hostaboat/alarm_clock/docs/alarm_clock.tex

\documentclass[12pt]{report}

%\usepackage{appendix}

\usepackage[margin=2cm]{geometry}
\geometry{letterpaper}
\setlength{\parindent}{0em}

\usepackage{array,booktabs}

\newcommand{\wood}{Bubinga}
\newcommand{\front}{aluminum}
\newcommand{\project}{Boogie Box}

%%%%%%%%%%%%%%%%%%%%%%%%%%%%%%%%%%%%%%%%%%%%%%%%%%%%%%%%%%%%%%%%%%%%%%%%%%%%%%%%
% Fonts
\usepackage{fontspec}

\newfontfamily\qag{TeX Gyre Adventor}
\newfontfamily\qbk{TeX Gyre Bonum}
\newfontfamily\ssfont[
  Path = fonts/,
  Extension = .ttf,
  UprightFont = *-Italic,
  ItalicFont = *-Italic,
  BoldFont = *-Italic,
  BoldItalicFont = *-Italic,
  Scale = 1.5,
]{DSEG7Classic}
\newfontfamily\ssfontinline[
  Path = fonts/,
  Extension = .ttf,
  UprightFont = *-Italic,
  ItalicFont = *-Italic,
  BoldFont = *-Italic,
  BoldItalicFont = *-Italic,
  Scale = 0.8,
]{DSEG7Classic}
\newfontfamily\ssfontsym[
  Path = fonts/,
  Extension = .ttf,
  UprightFont = *-Italic,
  ItalicFont = *-Italic,
  BoldFont = *-Italic,
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
\begin{tikzpicture}[baseline]
  \node[anchor=base,fill=black!80,draw=black,inner sep=0.7mm,rounded corners=0.5mm]
    {\color{white} \phantom{\ssfontsym #1}};
  \node[anchor=base,inner sep=0.7mm,rounded corners=0.5mm]
    {\color{white} \ssfontsym #2};
\end{tikzpicture}}

% {phantom text}{text}
\newcommand{\sSSDl}[2]{%
\begin{tikzpicture}[baseline]
  \node[anchor=base,fill=black!80,draw=black,inner sep=4pt,rounded corners=0.5mm]
    {\color{white} \phantom{\ssfont #1}};
  \node[anchor=base,inner sep=4pt,rounded corners=0.5mm]
    {\color{white} \ssfont #2};
\end{tikzpicture}}

% For inline text
\newcommand{\sD}[1]{{\sSSD{8.8.:8.8.}{#1}}}
\newcommand{\sDs}[1]{{\sSSD{8}{#1}}}
\newcommand{\symD}[1]{{\symSSD{8.8.:8.8.}{#1}}}

% For figures
\newcommand{\sDl}[1]{{\sSSDl{8.8.:8.8.}{#1}}}
\newcommand{\sDls}[1]{{\sSSDl{8}{#1}}}
\newcommand{\figD}[2]{%
\begin{table}[H]
\ers{0.1}
\centering
\begin{tabu}{c}
\sDl{#1} \\
\scriptsize #2 \\
\end{tabu}
\end{table}}

\newcommand{\figDT}[4]{%
\begin{table}[H]
\ers{0.1}
\centering
\begin{tabu} to 4in {X[1,c,m] X[1,c,m]}
\sDl{#1} & \sDl{#3} \\
\scriptsize #2 & \scriptsize #4 \\
\end{tabu}
\end{table}}

%%%%%%%%%%%%%%%%%%%%%%%%%%%%%%%%%%%%%%%%%%%%%%%%%%%%%%%%%%%%%%%%%%%%%%%%%%%%%%%%

%%%%%%%%%%%%%%%%%%%%%%%%%%%%%%%%%%%%%%%%%%%%%%%%%%%%%%%%%%%%%%%%%%%%%%%%%%%%%%%%
% Color Symbols
%%%%%%%%%%%%%%%%%%%%%%%%%%%%%%%%%%%%%%%%%%%%%%%%%%%%%%%%%%%%%%%%%%%%%%%%%%%%%%%%
\newcommand{\symColor}[3]{% <--- XXX Remove space before comment marker to smoosh
%\begin{tikzpicture}[overlay]
\begin{tikzpicture}[baseline=2]
  %\node[fill=#1,draw=black,inner sep=3pt,anchor=text,rectangle,rounded corners=0.5mm]
    %at (0.06,0.03) {\color{#2} \fontTGA{n}{#3}};
  \draw[fill=#1,draw=black,inner sep=1mm,rectangle,rounded corners=0.5mm]
    (0,0) rectangle node {\color{#2} \fontTGA{ss}{#3}} (1.7,0.4);
\end{tikzpicture} % <--- XXX Remove space before comment marker to smoosh
%\phantom{\fontTGA{n}{GGGGGG}}} % <--- XXX Remove space before comment marker to smoosh
} % <--- XXX Remove space before comment marker to smoosh

\newcommand{\cBl}{\symColor{blue}{white}{BLUE}}
\newcommand{\cGr}{\symColor{green}{black}{GREEN}}
\newcommand{\cYe}{\symColor{yellow}{black}{YELLOW}}
\newcommand{\cOr}{\symColor{orange}{black}{ORANGE}}
\newcommand{\cRe}{\symColor{red}{white}{RED}}
\newcommand{\cPu}{\symColor{violet}{white}{PURPLE}}
\newcommand{\cPi}{\symColor{pink}{white}{PINK}}

\newcommand{\cCol}[3]{\symColor{#1}{#2}{#3}}

%%%%%%%%%%%%%%%%%%%%%%%%%%%%%%%%%%%%%%%%%%%%%%%%%%%%%%%%%%%%%%%%%%%%%%%%%%%%%%%%
\newcommand{\ddfrac}[2]{\frac{\displaystyle #1}{\displaystyle #2}}

\setlength{\fboxsep}{12pt}

\newcommand{\danger}[1]{\begin{center}\fbox{%
\begin{minipage}{0.94\textwidth}%
{\raisebox{-1.1mm}{} #1}%
\end{minipage}}\end{center}}

\newcommand{\warning}[1]{\begin{center}\fbox{%
\begin{minipage}{0.94\textwidth}%
{\raisebox{-1.1mm}{} #1}%
\end{minipage}}\end{center}}

\newcommand{\info}[1]{\begin{center}\fbox{%
\begin{minipage}{0.94\textwidth}%
{\raisebox{-1.2mm}{} #1}%
\end{minipage}}\end{center}}

\newcommand{\cbox}[1]{\begin{center}\fcolorbox{black!20}{black!2}{%
\begin{minipage}{0.95\textwidth}#1\end{minipage}}\end{center}}

\newcommand{\steps}[2]{\begin{center}\begin{tcolorbox}[breakable, enhanced]%
\par\medskip%
{\parbox{\textwidth}{\centering \thbi{#1}}} \newline #2%
\end{tcolorbox}\end{center}}

%%%%%%%%%%%%%%%%%%%%%%%%%%%%%%%%%%%%%%%%%%%%%%%%%%%%%%%%%%%%%%%%%%%%%%%%%%%%%%%%

%%%%%%%%%%%%%%%%%%%%%%%%%%%%%%%%%%%%%%%%%%%%%%%%%%%%%%%%%%%%%%%%%%%%%%%%%%%%%%%%
% Title Info
%\title{}
%\author{}
%\date{\today}
%%%%%%%%%%%%%%%%%%%%%%%%%%%%%%%%%%%%%%%%%%%%%%%%%%%%%%%%%%%%%%%%%%%%%%%%%%%%%%%%

%%%%%%%%%%%%%%%%%%%%%%%%%%%%%%%%%%%%%%%%%%%%%%%%%%%%%%%%%%%%%%%%%%%%%%%%%%%%%%%%
% Begin Document %%%%%%%%%%%%%%%%%%%%%%%%%%%%%%%%%%%%%%%%%%%%%%%%%%%%%%%%%%%%%%%
%%%%%%%%%%%%%%%%%%%%%%%%%%%%%%%%%%%%%%%%%%%%%%%%%%%%%%%%%%%%%%%%%%%%%%%%%%%%%%%%
\begin{document}

\thispagestyle{empty}

\begin{table}[H]
\begin{tabu}{X[1,l,m] X[1,r,m]}
  \fontTGA{h}{\bfseries \project{}}
    & \fontTGA{ss}{Designed, coded and assembled by Todd Wease} \\
\end{tabu}
\end{table}

\begin{table}[H]
\ers{3}
\begin{tabu}{X[1,l,m] X[1,l,m]}
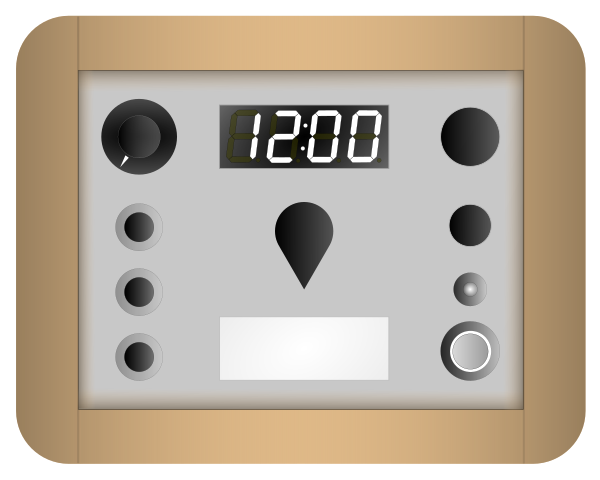
[picture p26: docs/images/alarm_clock.png]
  \multirow{5}{*}{}
    & \fontTGA{n}{Portable with Rechargeable Lithium Ion Battery} \\
  & \fontTGA{n}{USB connectivity allows for managing music on the device} \\
  & \fontTGA{n}{USB Micro port also used for powering and charging} \\
  & \fontTGA{n}{Low Battery Indicator} \\
  & \fontTGA{n}{Controllable Display and Lighting brightness} \\
\end{tabu}
\end{table}

\begin{table}[H]
\begin{tabu}{X[1,l,p] X[1,l,p]}
  \fontTGA{s}{\bfseries Clock}
  \footnotesize \qag
  \begin{itemize}[label=, leftmargin=1pt, itemsep=1pt]
    \item Date \& Time
    \item 12 or 24 Hour Time Format
    \item Configurable Daylight Saving Time
    \item Coin Cell Battery backup keeps time when device is unpowered
  \end{itemize}
  &
  \fontTGA{s}{\bfseries Alarm}
  \footnotesize \qag
  \begin{itemize}[label=, leftmargin=1pt, itemsep=1pt]
    \item Wake to Beeper or Audio
    \item Touch to Snooze
    \item Configurable Snooze Time
    \item Configurable Auto-Stop Timers
  \end{itemize}
\end{tabu}
\end{table}

\begin{table}[H]
\begin{tabu}{X[1,l,p] X[1,l,p]}
  \fontTGA{s}{\bfseries Audio}
  \footnotesize \qag
  \begin{itemize}[label=, leftmargin=1pt, itemsep=1pt]
    \item Dedicated Conrols
      \begin{itemize}[label=-, leftmargin=*, topsep=0mm, itemsep=0mm]
        \item Play \& Pause
        \item Skip Forward Tracks
        \item Skip Back \& Rewind Tracks
      \end{itemize}
    \item Stop function for extra power savings
    \item Direct track selection using Touch
  \end{itemize}
  &
  \fontTGA{s}{\bfseries Timer}
  \footnotesize \qag
  \begin{itemize}[label=, leftmargin=1pt, itemsep=1pt]
    \item Up to \textasciitilde100 hours
    \item Touch to stop alerting when done
    \item Countdown LED lighting
    \item Toggle display between Timer / Clock
  \end{itemize}

\end{tabu}
\end{table}

\begin{table}[H]
\begin{tabu}{X[1.3,l,p] X[1,l,p] X[1.5,l,p]}
  \fontTGA{s}{\bfseries Touch}
  \footnotesize \qag
  \begin{itemize}[label=, leftmargin=1pt, itemsep=1pt]
    \item Capacitive Touch Sensing
    \item Calibration and Tuning
    \item Configurable Sensitivity
  \end{itemize}
  &
  \fontTGA{s}{\bfseries Night Light}
  \footnotesize \qag
  \begin{itemize}[label=, leftmargin=1pt, itemsep=1pt]
    \item Up to 4 colors
      \begin{itemize}[label=-, leftmargin=*, topsep=0mm, itemsep=0mm]
        \item One White
        \item 3 Configurable
      \end{itemize}
    \item Lighting Animations
  \end{itemize}
  &
  \fontTGA{s}{\bfseries Power}
  \footnotesize \qag
  \begin{itemize}[label=, leftmargin=1pt, itemsep=1pt]
    \item Prolong battery charge when idle
      \begin{itemize}[label=-, leftmargin=*, topsep=0mm, itemsep=0mm]
        \item Two low power states
        \item Auto-stop Audio
      \end{itemize}
    \item All idle timers configurable
    \item Touch to force into Sleep state
  \end{itemize}

\end{tabu}
\end{table}

\fontTGA{t}{\today}

%\maketitle

\pagebreak

\tableofcontents
\listoffigures
\listoftables

%%%%%%%%%%%%%%%%%%%%%%%%%%%%%%%%%%%%%%%%%%%%%%%%%%%%%%%%%%%%%%%%%%%%%%%%%%%%%%%%
% Getting Started
%%%%%%%%%%%%%%%%%%%%%%%%%%%%%%%%%%%%%%%%%%%%%%%%%%%%%%%%%%%%%%%%%%%%%%%%%%%%%%%%
%\part{Getting Started} \label{Getting Started}
%
%\begin{table}[H]
%\ers{3}
%\centering
%\begin{tabu}{ X[2,l,m] | X[1,c,m]  }
%  \thrule
%  \thbi{Action} & \thbi{Section} \\ \mrule
%  Familiarize yourself with the enclosure and controls.
%    & \hyperref[Enclosure]{Enclosure \& Controls} \\
%  Familiarize yourself with the general operation of the device.
%    & \hyperref[Operation]{Operation} \\
%  Set the clock.
%    & \hyperref[Set Clock]{\mSC{n}} \\
%  Enable and calibrate \cTS{f}.
%    & \hyperref[Touch Settings]{\mTS{n}} \\
%  \bhrule
%\end{tabu}
%\end{table}

%%%%%%%%%%%%%%%%%%%%%%%%%%%%%%%%%%%%%%%%%%%%%%%%%%%%%%%%%%%%%%%%%%%%%%%%%%%%%%%%
% Enclosure
%%%%%%%%%%%%%%%%%%%%%%%%%%%%%%%%%%%%%%%%%%%%%%%%%%%%%%%%%%%%%%%%%%%%%%%%%%%%%%%%
\input{enclosure.tex}

%%%%%%%%%%%%%%%%%%%%%%%%%%%%%%%%%%%%%%%%%%%%%%%%%%%%%%%%%%%%%%%%%%%%%%%%%%%%%%%%
% Operation
%%%%%%%%%%%%%%%%%%%%%%%%%%%%%%%%%%%%%%%%%%%%%%%%%%%%%%%%%%%%%%%%%%%%%%%%%%%%%%%%
\input{operation.tex}

%%%%%%%%%%%%%%%%%%%%%%%%%%%%%%%%%%%%%%%%%%%%%%%%%%%%%%%%%%%%%%%%%%%%%%%%%%%%%%%%
% Components
%%%%%%%%%%%%%%%%%%%%%%%%%%%%%%%%%%%%%%%%%%%%%%%%%%%%%%%%%%%%%%%%%%%%%%%%%%%%%%%%
\part{Components} \label{Components}
\input{usb.tex}
\input{audio.tex}
\input{alarm.tex}
\input{power.tex}

%%%%%%%%%%%%%%%%%%%%%%%%%%%%%%%%%%%%%%%%%%%%%%%%%%%%%%%%%%%%%%%%%%%%%%%%%%%%%%%%
% Primary Modes
%%%%%%%%%%%%%%%%%%%%%%%%%%%%%%%%%%%%%%%%%%%%%%%%%%%%%%%%%%%%%%%%%%%%%%%%%%%%%%%%
\part{Primary Modes} \label{Primary Modes}
\input{clock.tex}
\input{set_alarm.tex}
\input{timer.tex}

%%%%%%%%%%%%%%%%%%%%%%%%%%%%%%%%%%%%%%%%%%%%%%%%%%%%%%%%%%%%%%%%%%%%%%%%%%%%%%%%
% Secondary Modes
%%%%%%%%%%%%%%%%%%%%%%%%%%%%%%%%%%%%%%%%%%%%%%%%%%%%%%%%%%%%%%%%%%%%%%%%%%%%%%%%
\part{Secondary Modes} \label{Secondary Modes}
\input{set_clock.tex}
\input{power_settings.tex}

%%%%%%%%%%%%%%%%%%%%%%%%%%%%%%%%%%%%%%%%%%%%%%%%%%%%%%%%%%%%%%%%%%%%%%%%%%%%%%%%
% Tertiary Modes
%%%%%%%%%%%%%%%%%%%%%%%%%%%%%%%%%%%%%%%%%%%%%%%%%%%%%%%%%%%%%%%%%%%%%%%%%%%%%%%%
\part{Tertiary Modes} \label{Tertiary Modes}
\input{touch_settings.tex}
\input{set_night_light.tex}

%%%%%%%%%%%%%%%%%%%%%%%%%%%%%%%%%%%%%%%%%%%%%%%%%%%%%%%%%%%%%%%%%%%%%%%%%%%%%%%%
% Maintenance
%%%%%%%%%%%%%%%%%%%%%%%%%%%%%%%%%%%%%%%%%%%%%%%%%%%%%%%%%%%%%%%%%%%%%%%%%%%%%%%%
\input{maintenance.tex}

%%%%%%%%%%%%%%%%%%%%%%%%%%%%%%%%%%%%%%%%%%%%%%%%%%%%%%%%%%%%%%%%%%%%%%%%%%%%%%%%
% Troubleshooting
%%%%%%%%%%%%%%%%%%%%%%%%%%%%%%%%%%%%%%%%%%%%%%%%%%%%%%%%%%%%%%%%%%%%%%%%%%%%%%%%
\input{troubleshooting.tex}

%%%%%%%%%%%%%%%%%%%%%%%%%%%%%%%%%%%%%%%%%%%%%%%%%%%%%%%%%%%%%%%%%%%%%%%%%%%%%%%%
% Appendix
%%%%%%%%%%%%%%%%%%%%%%%%%%%%%%%%%%%%%%%%%%%%%%%%%%%%%%%%%%%%%%%%%%%%%%%%%%%%%%%%
\input{appendix.tex}

\end{document}
