hostaboat/alarm_clock/docs/images/circuit_board.png

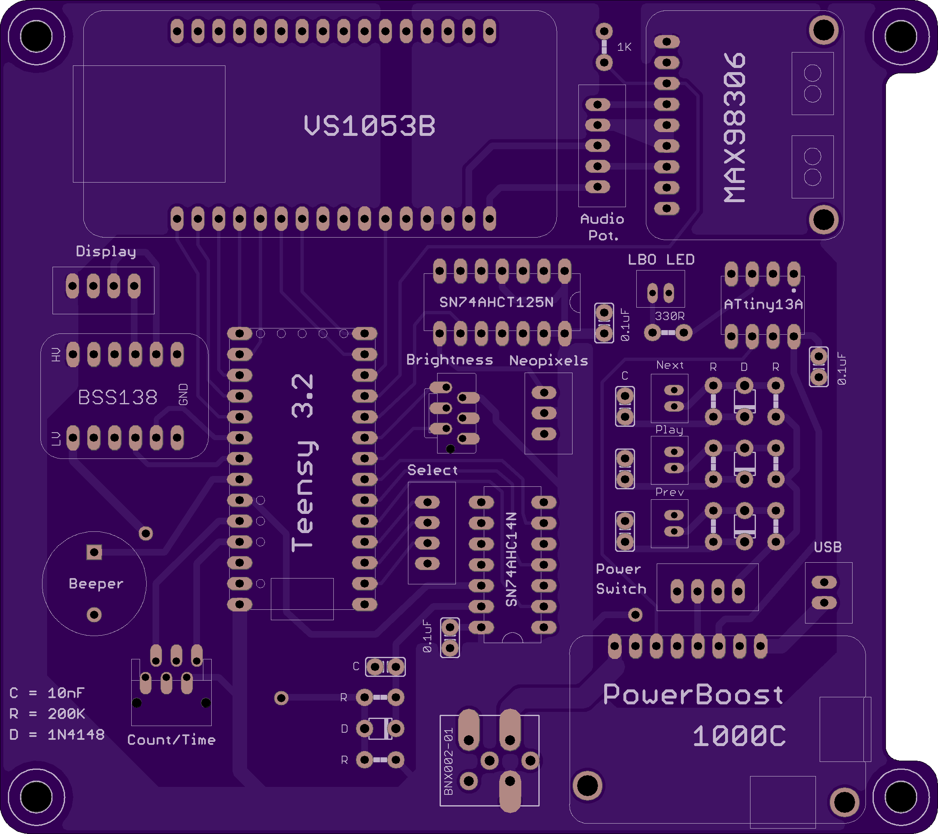
docs/images/circuit_board.png
