hostaboat/alarm_clock/docs/images/touch_vs_no_touch.png

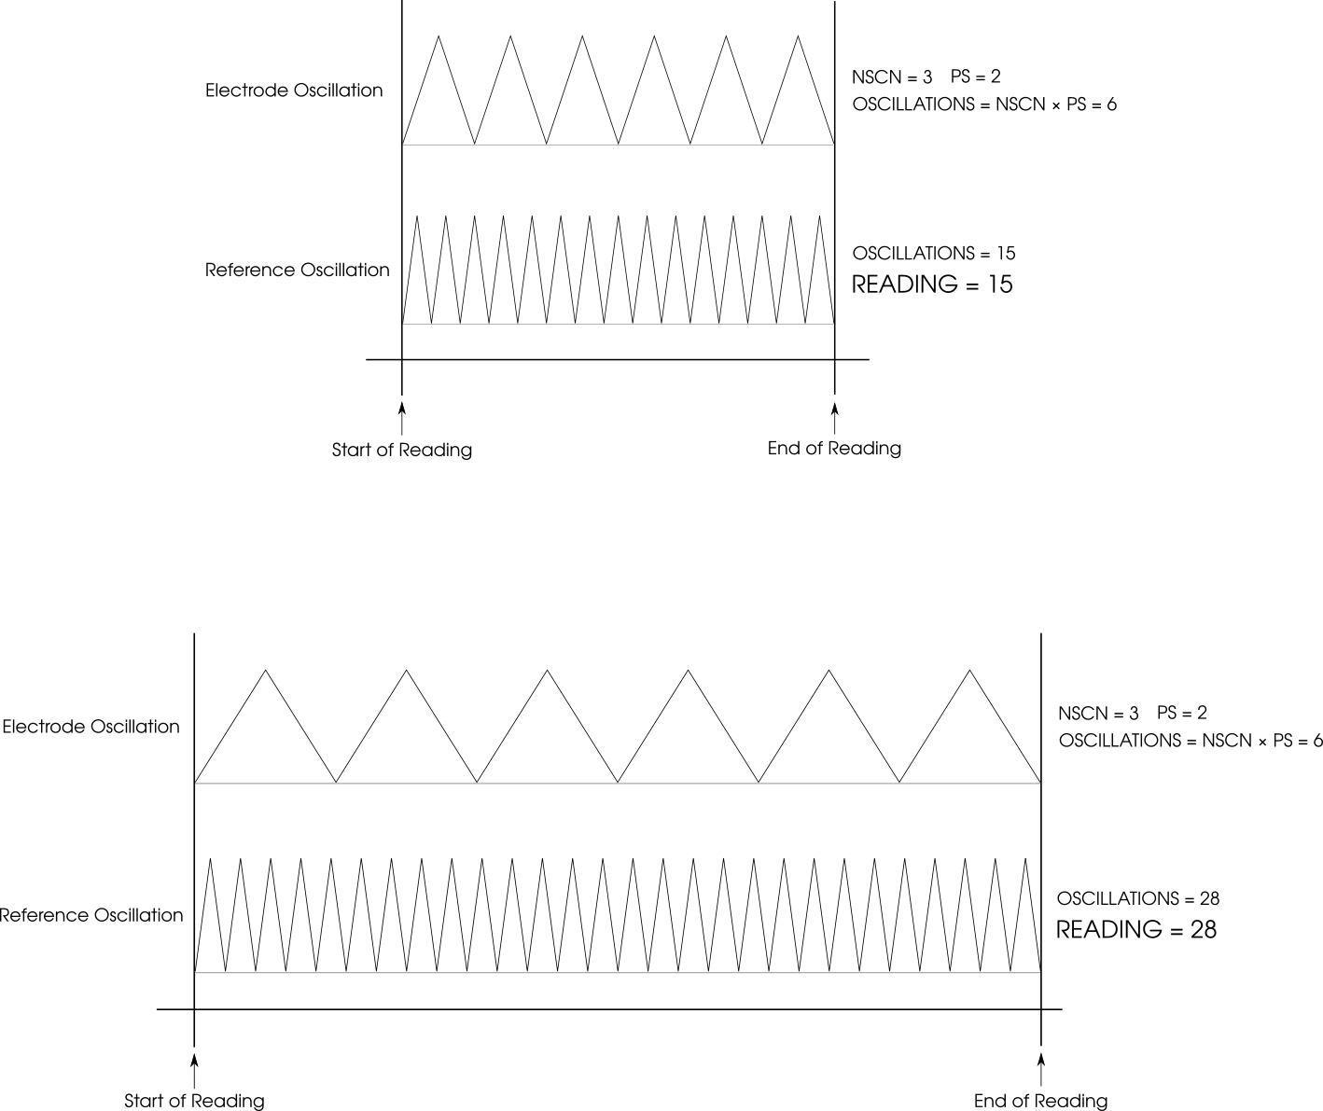
docs/images/touch_vs_no_touch.png
