hostaboat/alarm_clock/spi_cta.cpp

#include "types.h"
#include "spi.h"
#include "spi_cta.h"

#ifndef F_BUS
# error "F_BUS not defined"
#endif

////////////////////////////////////////////////////////////////////////////////
// Clock and Transfer Attributes
////////////////////////////////////////////////////////////////////////////////
// uint32_t sck   - frequency in Hz
// uint32_t t_csc - the delay between assertion of PCS and the first edge of SCK
// uint32_t t_asc - the delay between the last edge of SCK and negation of PCS
// uint32_t t_dt  - the time between negation of PCS and next assertion of PCS
// This function returns the relevant bits for use in the CTAR field.
uint32_t spi_cta(uint32_t sck, uint32_t t_csc, uint32_t t_asc, uint32_t t_dt)
{
    return (spi_sck(sck)
            | spi_pcs_to_sck_delay(t_csc)
            | spi_delay_after_sck(t_asc)
            | spi_delay_after_transfer(t_dt));
}

////////////////////////////////////////////////////////////////////////////////
// SCK baud rate to be used for SPI transfers.
// Given the frequency in Hz argument passed in, this function
// returns the relevant bits for use in the CTAR field.
uint32_t spi_sck(uint32_t frequency)
{
    uint32_t sck;

#if F_BUS == 48000000
    if (frequency >= 24000000)
        sck = SPI_CTAR_BR(0) | SPI_CTAR_PBR(0) | SPI_CTAR_DBR;
    else if (frequency >= 12000000)
        sck = SPI_CTAR_BR(0) | SPI_CTAR_PBR(0);
    else if (frequency >= 8000000)
        sck = SPI_CTAR_BR(0) | SPI_CTAR_PBR(1);
    else if (frequency >= 6000000)
        sck = SPI_CTAR_BR(1) | SPI_CTAR_PBR(0);
    else if (frequency >= 4800000)
        sck = SPI_CTAR_BR(0) | SPI_CTAR_PBR(2);
    else if (frequency >= 4000000)
        sck = SPI_CTAR_BR(1) | SPI_CTAR_PBR(1);
    else if (frequency >= 3428571)
        sck = SPI_CTAR_BR(0) | SPI_CTAR_PBR(3);
    else if (frequency >= 3000000)
        sck = SPI_CTAR_BR(3) | SPI_CTAR_PBR(0);
    else if (frequency >= 2666666)
        sck = SPI_CTAR_BR(2) | SPI_CTAR_PBR(1);
    else if (frequency >= 2400000)
        sck = SPI_CTAR_BR(1) | SPI_CTAR_PBR(2);
    else if (frequency >= 2000000)
        sck = SPI_CTAR_BR(3) | SPI_CTAR_PBR(1);
    else if (frequency >= 1714285)
        sck = SPI_CTAR_BR(1) | SPI_CTAR_PBR(3);
    else if (frequency >= 1600000)
        sck = SPI_CTAR_BR(2) | SPI_CTAR_PBR(2);
    else if (frequency >= 1500000)
        sck = SPI_CTAR_BR(4) | SPI_CTAR_PBR(0);
    else if (frequency >= 1200000)
        sck = SPI_CTAR_BR(3) | SPI_CTAR_PBR(2);
    else if (frequency >= 1142857)
        sck = SPI_CTAR_BR(2) | SPI_CTAR_PBR(3);
    else if (frequency >= 1000000)
        sck = SPI_CTAR_BR(4) | SPI_CTAR_PBR(1);
    else if (frequency >= 857142)
        sck = SPI_CTAR_BR(3) | SPI_CTAR_PBR(3);
    else if (frequency >= 750000)
        sck = SPI_CTAR_BR(5) | SPI_CTAR_PBR(0);
    else if (frequency >= 600000)
        sck = SPI_CTAR_BR(4) | SPI_CTAR_PBR(2);
    else if (frequency >= 500000)
        sck = SPI_CTAR_BR(5) | SPI_CTAR_PBR(1);
    else if (frequency >= 428571)
        sck = SPI_CTAR_BR(4) | SPI_CTAR_PBR(3);
    else if (frequency >= 375000)
        sck = SPI_CTAR_BR(6) | SPI_CTAR_PBR(0);
    else if (frequency >= 300000)
        sck = SPI_CTAR_BR(5) | SPI_CTAR_PBR(2);
    else if (frequency >= 250000)
        sck = SPI_CTAR_BR(6) | SPI_CTAR_PBR(1);
    else if (frequency >= 214285)
        sck = SPI_CTAR_BR(5) | SPI_CTAR_PBR(3);
    else if (frequency >= 187500)
        sck = SPI_CTAR_BR(7) | SPI_CTAR_PBR(0);
    else if (frequency >= 150000)
        sck = SPI_CTAR_BR(6) | SPI_CTAR_PBR(2);
    else if (frequency >= 125000)
        sck = SPI_CTAR_BR(7) | SPI_CTAR_PBR(1);
    else if (frequency >= 107142)
        sck = SPI_CTAR_BR(6) | SPI_CTAR_PBR(3);
    else if (frequency >= 93750)
        sck = SPI_CTAR_BR(8) | SPI_CTAR_PBR(0);
    else if (frequency >= 75000)
        sck = SPI_CTAR_BR(7) | SPI_CTAR_PBR(2);
    else if (frequency >= 62500)
        sck = SPI_CTAR_BR(8) | SPI_CTAR_PBR(1);
    else if (frequency >= 53571)
        sck = SPI_CTAR_BR(7) | SPI_CTAR_PBR(3);
    else if (frequency >= 46875)
        sck = SPI_CTAR_BR(9) | SPI_CTAR_PBR(0);
    else if (frequency >= 37500)
        sck = SPI_CTAR_BR(8) | SPI_CTAR_PBR(2);
    else if (frequency >= 31250)
        sck = SPI_CTAR_BR(9) | SPI_CTAR_PBR(1);
    else if (frequency >= 26785)
        sck = SPI_CTAR_BR(8) | SPI_CTAR_PBR(3);
    else if (frequency >= 23437)
        sck = SPI_CTAR_BR(10) | SPI_CTAR_PBR(0);
    else if (frequency >= 18750)
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
    else if (frequency >= 2571428)
        sck = SPI_CTAR_BR(0) | SPI_CTAR_PBR(3);
    else if (frequency >= 2250000)
        sck = SPI_CTAR_BR(3) | SPI_CTAR_PBR(0);
    else if (frequency >= 2000000)
        sck = SPI_CTAR_BR(2) | SPI_CTAR_PBR(1);
    else if (frequency >= 1800000)
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
